AHA-Taiwan/2019-Taitung-BNES-Reading-Boat/001. Blueprint/2D PDF/2D PNG/1 (5).png

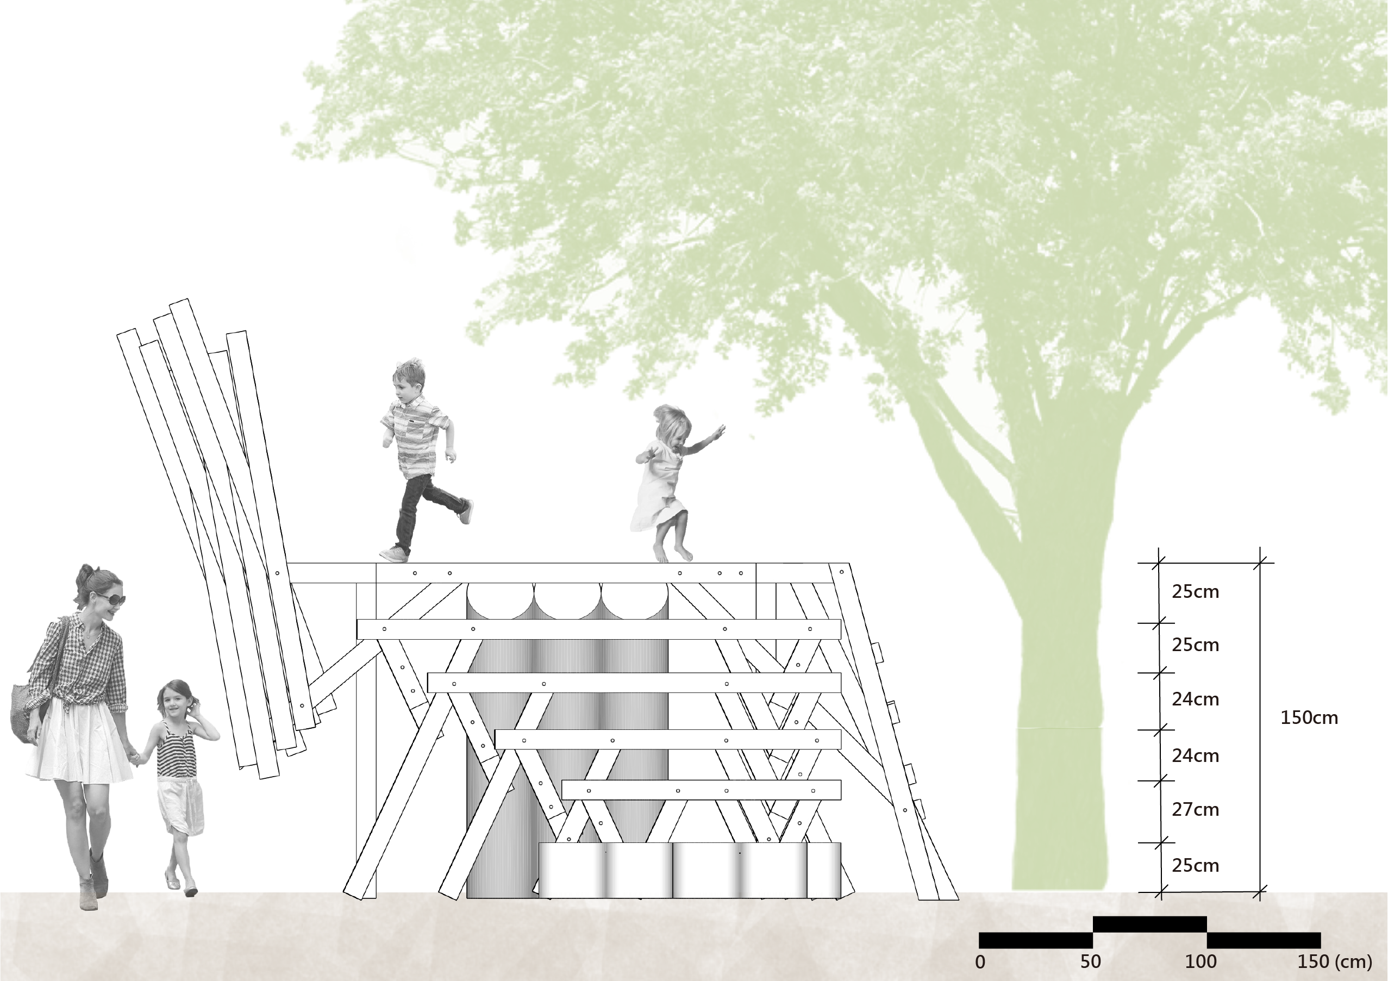
001. Blueprint/2D PDF/2D PNG/1 (5).png
